sigpwny/fallctf-2025-badge/dev/assets/planets.png

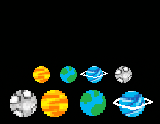
dev/assets/planets.png
