sigpwny/fallctf-2025-badge/dev/assets/sponsors.png

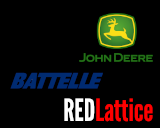
dev/assets/sponsors.png
