sigpwny/fallctf-2025-badge/dev/assets/undecided_faction.png

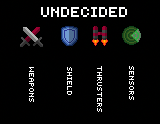
dev/assets/undecided_faction.png
