sigpwny/fallctf-2025-badge/board-setup/frozen_files/ST7735.py

#driver for Sainsmart 1.8" TFT display ST7735
#Translated by Guy Carver from the ST7735 sample code.
#Modirfied for micropython-esp32 by boochow 

import machine
import time

#TFTRotations and TFTRGB are bits to set
# on MADCTL to control display rotation/color layout
#Looking at display with pins on top.
#00 = upper left printing right
#10 = does nothing (MADCTL_ML)
#20 = upper left printing down (backwards) (Vertical flip)
#40 = upper right printing left (backwards) (X Flip)
#80 = lower left printing right (backwards) (Y Flip)
#04 = (MADCTL_MH)

#60 = 90 right rotation
#C0 = 180 right rotation
#A0 = 270 right rotation
TFTRotations = [0x00, 0x60, 0xC0, 0xA0]
TFTBGR = 0x08 #When set color is bgr else rgb.
TFTRGB = 0x00

#@micropython.native
def clamp( aValue, aMin, aMax ) :
  return max(aMin, min(aMax, aValue))

#@micropython.native
def TFTColor( aR, aG, aB ) :
  '''Create a 16 bit rgb value from the given R,G,B from 0-255.
     This assumes rgb 565 layout and will be incorrect for bgr.'''
  val = ((aR & 0xF8) << 8) | ((aG & 0xFC) << 3) | (aB >> 3)
  # convert endianess for framebuf
  return ((val & 0xFF) << 8) | (val >> 8)

ScreenSize = (130, 161)

class TFT(object) :
  """Sainsmart TFT 7735 display driver."""

  NOP = 0x0
  SWRESET = 0x01
  RDDID = 0x04
  RDDST = 0x09

  SLPIN  = 0x10
  SLPOUT  = 0x11
  PTLON  = 0x12
  NORON  = 0x13

  INVOFF = 0x20
  INVON = 0x21
  DISPOFF = 0x28
  DISPON = 0x29
  CASET = 0x2A
  RASET = 0x2B
  RAMWR = 0x2C
  RAMRD = 0x2E

  VSCRDEF = 0x33
  VSCSAD = 0x37

  COLMOD = 0x3A
  MADCTL = 0x36

  FRMCTR1 = 0xB1
  FRMCTR2 = 0xB2
  FRMCTR3 = 0xB3
  INVCTR = 0xB4
  DISSET5 = 0xB6

  PWCTR1 = 0xC0
  PWCTR2 = 0xC1
  PWCTR3 = 0xC2
  PWCTR4 = 0xC3
  PWCTR5 = 0xC4
  VMCTR1 = 0xC5

  RDID1 = 0xDA
  RDID2 = 0xDB
  RDID3 = 0xDC
  RDID4 = 0xDD

  PWCTR6 = 0xFC

  GMCTRP1 = 0xE0
  GMCTRN1 = 0xE1

  BLACK = 0
  RED = TFTColor(0xFF, 0x00, 0x00)
  MAROON = TFTColor(0x80, 0x00, 0x00)
  GREEN = TFTColor(0x00, 0xFF, 0x00)
  FOREST = TFTColor(0x00, 0x80, 0x80)
  BLUE = TFTColor(0x00, 0x00, 0xFF)
  NAVY = TFTColor(0x00, 0x00, 0x80)
  CYAN = TFTColor(0x00, 0xFF, 0xFF)
  YELLOW = TFTColor(0xFF, 0xFF, 0x00)
  PURPLE = TFTColor(0xFF, 0x00, 0xFF)
  WHITE = TFTColor(0xFF, 0xFF, 0xFF)
  GRAY = TFTColor(0x80, 0x80, 0x80)

  @staticmethod
  def color( aR, aG, aB ) :
    '''Create a 565 rgb TFTColor value'''
    return TFTColor(aR, aG, aB)

  def __init__( self, spi, aDC, aReset, aCS, variant='red') :
    """aLoc SPI pin location is either 1 for 'X' or 2 for 'Y'.
       aDC is the DC pin and aReset is the reset pin."""
    self._size = ScreenSize
    self._offset = bytearray([0,0])
    self.rotate = 0                    #Vertical with top toward pins.
    self._rgb = True                   #color order of rgb.
    self.tfa = 0                       #top fixed area
    self.bfa = 0                       #bottom fixed area
    self.dc  = machine.Pin(aDC, machine.Pin.OUT, machine.Pin.PULL_DOWN)
    self.reset = machine.Pin(aReset, machine.Pin.OUT, machine.Pin.PULL_DOWN)
    self.cs = machine.Pin(aCS, machine.Pin.OUT, machine.Pin.PULL_DOWN)
    self.cs(1)
    self.spi = spi
    self.colorData = bytearray(2)
    self.windowLocData = bytearray(4)
    if variant == 'red':
        self._offset = [0, 0]
    elif variant == 'green':
        self._offset = [1, 2]
    elif variant == 'black':
        self._offset = [2, 3]

  def size( self ) :
    return self._size

#   @micropython.native
  def on( self, aTF = True ) :
    '''Turn display on or off.'''
    self._writecommand(TFT.DISPON if aTF else TFT.DISPOFF)

#   @micropython.native
  def rgb( self, aTF = True ) :
    '''True = rgb else bgr'''
    self._rgb = aTF
    self._setMADCTL()

#   @micropython.native
  def rotation( self, aRot ) :
    '''0 - 3. Starts vertical with top toward pins and rotates 90 deg
       clockwise each step.'''
    if (0 <= aRot < 4):
      rotchange = self.rotate ^ aRot
      self.rotate = aRot
      #If switching from vertical to horizontal swap x,y
      # (indicated by bit 0 changing).
      if (rotchange & 1):
        self._size =(self._size[1], self._size[0])
      self._setMADCTL()

  def image( self, x0, y0, x1, y1, data ) :
    self._setwindowloc((x0, y0), (x1, y1))
    self._writedata(data)

#   @micropython.native
  def _setwindowloc( self, aPos0, aPos1 ) :
    '''Set a rectangular area for drawing a color to.'''
    self._writecommand(TFT.CASET)            #Column address set.
    self.windowLocData[0] = self._offset[0]
    self.windowLocData[1] = self._offset[0] + int(aPos0[0])
    self.windowLocData[2] = self._offset[0]
    self.windowLocData[3] = self._offset[0] + int(aPos1[0])
    self._writedata(self.windowLocData)

    self._writecommand(TFT.RASET)            #Row address set.
    self.windowLocData[0] = self._offset[1]
    self.windowLocData[1] = self._offset[1] + int(aPos0[1])
    self.windowLocData[2] = self._offset[1]
    self.windowLocData[3] = self._offset[1] + int(aPos1[1])
    self._writedata(self.windowLocData)

    self._writecommand(TFT.RAMWR)            #Write to RAM.

  #@micropython.native
  def _writecommand( self, aCommand ) :
    '''Write given command to the device.'''
    self.dc(0)
    self.cs(0)
    self.spi.write(bytearray([aCommand]))
    self.cs(1)

  #@micropython.native
  def _writedata( self, aData ) :
    '''Write given data to the device.  This may be
       either a single int or a bytearray of values.'''
    self.dc(1)
    self.cs(0)
    self.spi.write(aData)
    self.cs(1)

  #@micropython.native
  def _setMADCTL( self ) :
    '''Set screen rotation and RGB/BGR format.'''
    self._writecommand(TFT.MADCTL)
    rgb = TFTRGB if self._rgb else TFTBGR
    self._writedata(bytearray([TFTRotations[self.rotate] | rgb]))

  #@micropython.native
  def _reset( self ) :
    '''Reset the device.'''
    self.dc(0)
    self.reset(1)
    time.sleep_us(500)
    self.reset(0)
    time.sleep_us(500)
    self.reset(1)
    time.sleep_us(500)

  #@micropython.native
  def initg( self ) :
    '''Initialize a green tab version.'''
    self._reset()

    self._writecommand(TFT.SWRESET)              #Software reset.
    time.sleep_us(150)
    self._writecommand(TFT.SLPOUT)               #out of sleep mode.
    time.sleep_us(255)

    data3 = bytearray([0x01, 0x2C, 0x2D])       #fastest refresh, 6 lines front, 3 lines back.
    self._writecommand(TFT.FRMCTR1)              #Frame rate control.
    self._writedata(data3)

    self._writecommand(TFT.FRMCTR2)              #Frame rate control.
    self._writedata(data3)

    data6 = bytearray([0x01, 0x2c, 0x2d, 0x01, 0x2c, 0x2d])
    self._writecommand(TFT.FRMCTR3)              #Frame rate control.
    self._writedata(data6)
    time.sleep_us(10)

    self._writecommand(TFT.INVCTR)               #Display inversion control
    self._writedata(bytearray([0x07]))
    self._writecommand(TFT.PWCTR1)               #Power control
    data3[0] = 0xA2
    data3[1] = 0x02
    data3[2] = 0x84
    self._writedata(data3)

    self._writecommand(TFT.PWCTR2)               #Power control
    self._writedata(bytearray([0xC5]))

    data2 = bytearray(2)
    self._writecommand(TFT.PWCTR3)               #Power control
    data2[0] = 0x0A   #Opamp current small
    data2[1] = 0x00   #Boost frequency
    self._writedata(data2)

    self._writecommand(TFT.PWCTR4)               #Power control
    data2[0] = 0x8A   #Opamp current small
    data2[1] = 0x2A   #Boost frequency
    self._writedata(data2)

    self._writecommand(TFT.PWCTR5)               #Power control
    data2[0] = 0x8A   #Opamp current small
    data2[1] = 0xEE   #Boost frequency
    self._writedata(data2)

    self._writecommand(TFT.VMCTR1)               #Power control
    self._writedata(bytearray([0x0E]))

    self._writecommand(TFT.INVOFF)

    self._setMADCTL()

    self._writecommand(TFT.COLMOD)
    self._writedata(bytearray([0x05]))

    self._writecommand(TFT.CASET)                #Column address set.
    self.windowLocData[0] = 0x00
    self.windowLocData[1] = 0x01                #Start at row/column 1.
    self.windowLocData[2] = 0x00
    self.windowLocData[3] = self._size[0] - 1
    self._writedata(self.windowLocData)

    self._writecommand(TFT.RASET)                #Row address set.
    self.windowLocData[3] = self._size[1] - 1
    self._writedata(self.windowLocData)

    dataGMCTRP = bytearray([0x02, 0x1c, 0x07, 0x12, 0x37, 0x32, 0x29, 0x2d, 0x29,
                            0x25, 0x2b, 0x39, 0x00, 0x01, 0x03, 0x10])
    self._writecommand(TFT.GMCTRP1)
    self._writedata(dataGMCTRP)

    dataGMCTRN = bytearray([0x03, 0x1d, 0x07, 0x06, 0x2e, 0x2c, 0x29, 0x2d, 0x2e,
                            0x2e, 0x37, 0x3f, 0x00, 0x00, 0x02, 0x10])
    self._writecommand(TFT.GMCTRN1)
    self._writedata(dataGMCTRN)

    self._writecommand(TFT.NORON)                #Normal display on.
    time.sleep_us(10)

    self._writecommand(TFT.DISPON)
    time.sleep_us(100)

    self.cs(1)
