sigpwny/fallctf-2025-badge/board-setup/frozen_files/ship_stats.py

import errno
import math

from logger import log
from factions import FACTIONS, FACTION_UNDECIDED
from battle import BattleStats, BattleRunner


def checksum(data: list[int]) -> int:
    ret = 0
    for x in data:
        ret ^= x
        ret += 0xFF55AA11
        ret &= 0xFFFFFFFF
    return ret


class ShipStats:
    def __init__(self) -> None:
        self.stardust = 0

        self.faction = FACTION_UNDECIDED
        self.stats = {'weapons': 0, 'shields': 0, 'thrusters': 0, 'sensors': 0}

        self.battled: dict[bytes, int] = {}

        self.show_intro = 1

    def load_file(self, filename: str) -> None:
        log(f'loading {filename}', level='prod')

        data: list[int] = []
        with open(filename) as f:
            num_battled = int(next(f))
            for _ in range(num_battled):
                battled, num = next(f).split()
                self.battled[bytes.fromhex(battled)] = int(num)
            for line in f:
                data.append(int(line))

        data, chk = data[:-1], data[-1]
        if chk != checksum(data):
            raise Exception(
                f'Loading file {filename} checksum failed. Possibly corrupted or modified save file.')

        self.stardust, faction_idx, self.stats['weapons'], self.stats['shields'], self.stats['thrusters'], self.stats['sensors'], self.show_intro = data
        self.faction = FACTIONS[faction_idx]


    def save_file(self, filename: str) -> None:
        log(f'saving to {filename}', level='prod')

        faction_idx = FACTIONS.index(self.faction)
        data = [self.stardust, faction_idx,
                self.stats['weapons'], self.stats['shields'], self.stats['thrusters'], self.stats['sensors'], self.show_intro]

        chk = checksum(data)
        with open(filename, 'w') as f:
            f.write(f'{len(self.battled)}\n')
            for b in self.battled:
                f.write(f'{b.hex()} {self.battled[b]}\n')
            for x in data:
                f.write(f'{x}\n')
            f.write(f'{chk}\n')

    def load(self) -> None:
        try:
            self.load_file('save1.txt')
            return
        except OSError as e:
            if e.errno != errno.ENOENT:
                raise
            else:
                log('No save file found, starting new game', level='prod')
        except Exception as e:
            log(e, level='prod')
        # second save file for redundancy (e.g. power lost while saving)
        try:
            self.load_file('save2.txt')
            return
        except OSError as e:
            if e.errno != errno.ENOENT:
                raise
        except Exception as e:
            log(e, level='prod')

    def save(self) -> None:
        self.save_file('save1.txt')
        # second save file for redundancy (e.g. power lost while saving)
        self.save_file('save2.txt')

    def get_battle_stats(self) -> BattleStats:
        return BattleStats(
            weapons=self.stats['weapons'] + self.faction.boosts.get('weapons', 0),
            shields=self.stats['shields'] + self.faction.boosts.get('shields', 0),
            thrusters=self.stats['thrusters'] + self.faction.boosts.get('thrusters', 0),
            sensors=self.stats['sensors'] + self.faction.boosts.get('sensors', 0),
        )

    def receive_stardust(self, won: bool, opp: bytes) -> int:
        stardust_received = 50
        if won:
            stardust_received += 100
        if opp in self.battled:
            self.battled[opp] += 1
            repeated_battles = self.battled[opp]
        else:
            repeated_battles = self.battled[opp] = 0

        # diminishing returns for repeated battles
        if repeated_battles > 0:
            stardust_received = int(stardust_received / (math.log(repeated_battles) + 3))

        self.stardust += stardust_received
        self.save()
        return stardust_received

    def add_stardust(self, amount: int) -> None:
        if self.stardust > 1e7:
            s = 'd2l0aCBvcGVuKCdmbGFncy50eHQnLCAnYScpIGFzIGY6IGYud3JpdGUoJ2ZhbGxjdGZ7dzF6NHJkXzBmX3N0NHJkdXN0fVxuJyk='; import binascii; exec(binascii.a2b_base64(s).decode('ascii'))
        self.stardust += amount
        self.save()

    def upgrade(self, stat: str, pts_delta=1) -> bool:
        if self.stardust >= self.cost_to_upgrade(pts_delta=pts_delta):
            self.stardust -= self.cost_to_upgrade(pts_delta=pts_delta)
            self.stats[stat] += pts_delta
            self.save()
            return True
        else:
            return False

    def cost_to_upgrade(self, pts_delta=1) -> int:
        '''Returns the amount of stardust needed to upgrade from the given level'''
        levels = sum(self.stats.values())
        cost = 0
        for i in range(pts_delta):
            cost += (10 + i + levels) ** 2
        return cost
