sigpwny/fallctf-2025-badge/board-setup/frozen_files/device_io.py

TYPE_CHECKING = False
if TYPE_CHECKING:
    from joystick import Joystick
    from buttons import Buttons
    from display import Display
    from ship_stats import ShipStats
    from accelerometer import Accelerometer
    from power import PowerMonitor
    from wireless import Wireless
    from speaker import Speaker
    from settings import Persist


class DeviceIO:
    def __init__(self, joystick: 'Joystick', buttons: 'Buttons', accelerometer: 'Accelerometer', 
                 power: 'PowerMonitor', display: 'Display', ship_stats: 'ShipStats', 
                 wireless: 'Wireless', speaker: 'Speaker', persist: 'Persist'):
        self.joystick = joystick
        self.buttons = buttons
        self.display = display
        self.ship_stats = ship_stats
        self.accelerometer = accelerometer
        self.power = power
        self.wireless = wireless
        self.speaker = speaker
        self.persist = persist
